m1geo/handifinder/Outputs/3d_render2.png

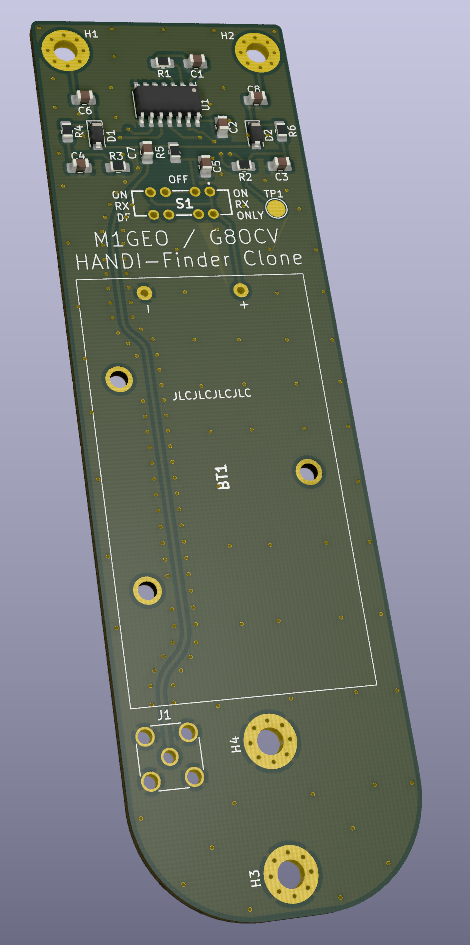
Outputs/3d_render2.png
